0ddjob/PMD_85/ROM_MEGAmodul/Kicad/PMD85_ROM_MEGA_Module.kicad_pcb

## KiCad design schematic/Kicad/Basic_setup/Basic_Setup.kicad_sch

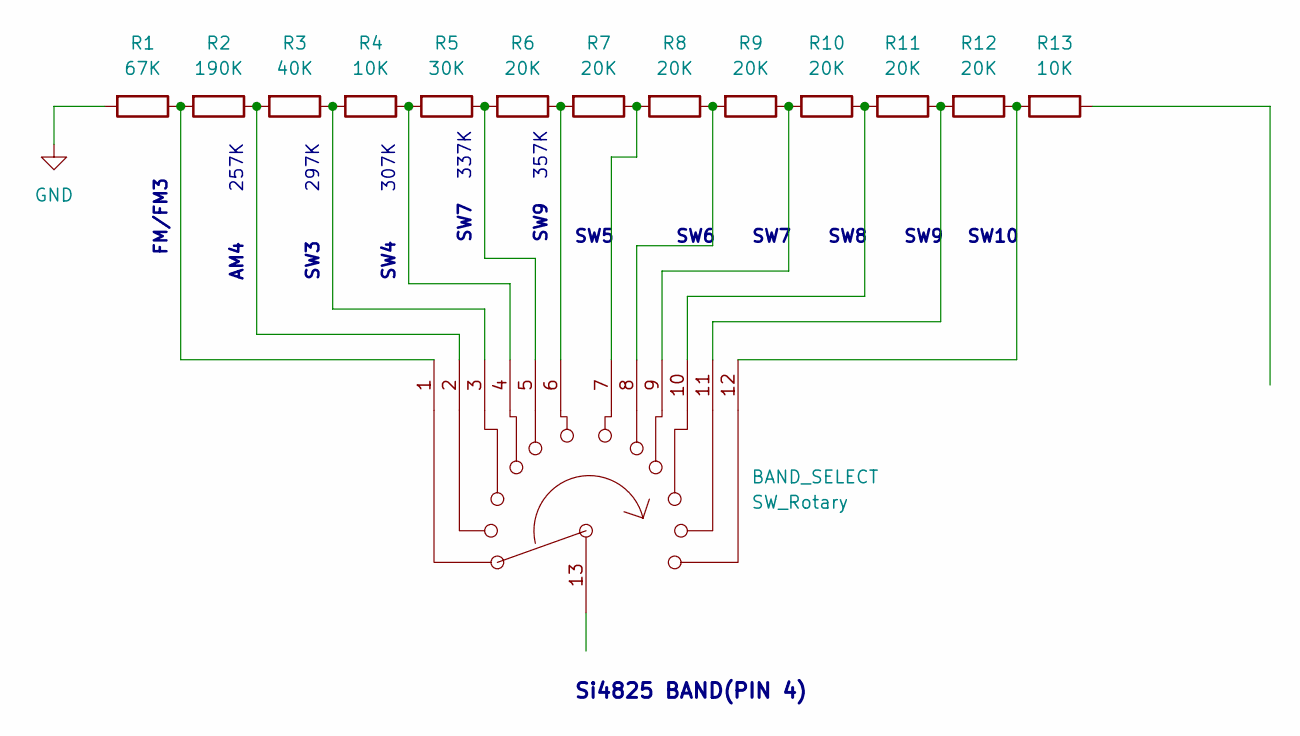
[picture p16: schematic Basic_Setup.kicad_sch]

Parts:
BAND_SELECT: SW_Rotary
R1: 67K
R2: 190K
R3: 40K
R4, R13: 10K
R5: 30K
R6, R7, R8, R9, R10, R11, R12: 20K

Connections:
GND: R1.2
unnamed: BAND_SELECT.1, R1.1, R2.2
unnamed: BAND_SELECT.2, R2.1, R3.2
unnamed: BAND_SELECT.3, R3.1, R4.2
unnamed: BAND_SELECT.4, R4.1, R5.2
unnamed: BAND_SELECT.5, R5.1, R6.2
unnamed: BAND_SELECT.6, R6.1, R7.2
unnamed: BAND_SELECT.7, R7.1, R8.2
unnamed: BAND_SELECT.8, R8.1, R9.2
unnamed: BAND_SELECT.9, R9.1, R10.2
unnamed: BAND_SELECT.10, R10.1, R11.2
unnamed: BAND_SELECT.11, R11.1, R12.2
unnamed: BAND_SELECT.12, R12.1, R13.2

Notes on the sheet:
SW7
Si4825 BAND(PIN 4)
337K
SW8
SW6
SW9
SW10
AM4
297K
357K
SW4
307K
257K
FM/FM3
SW3
SW5
